todbot/picostepseq/docs/picostepseq_assembly2.jpg

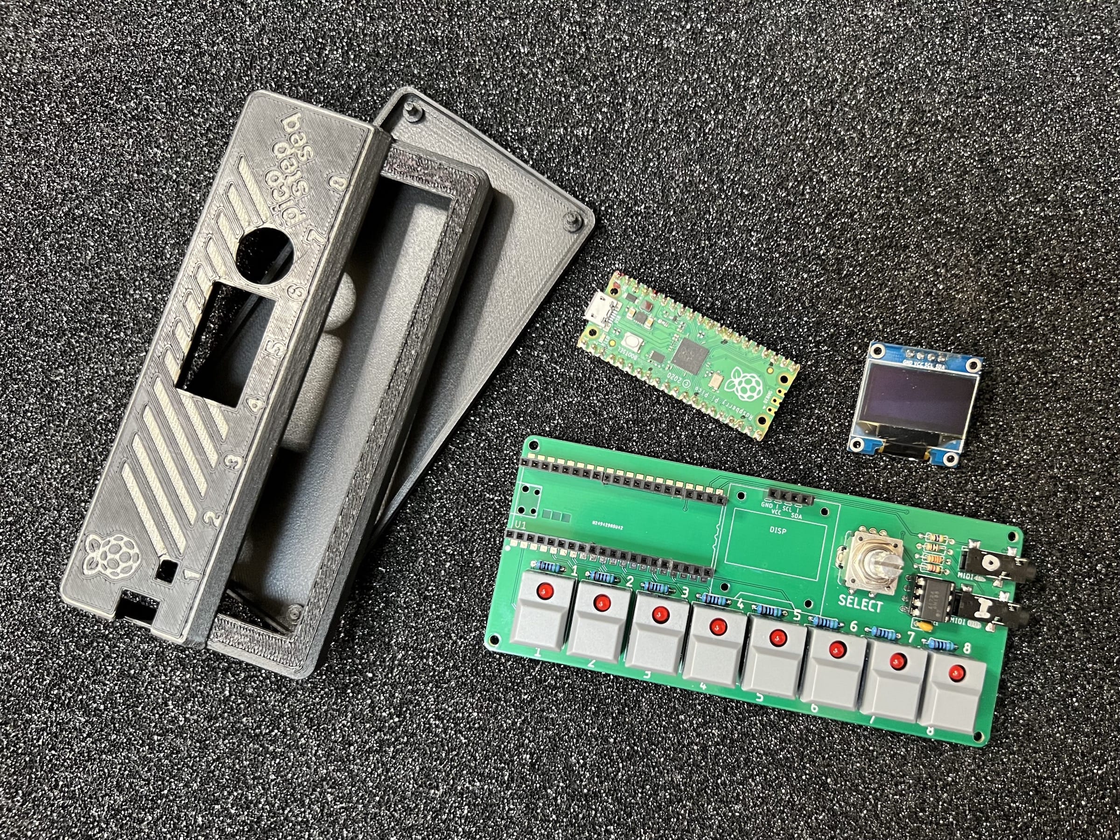
docs/picostepseq_assembly2.jpg
