todbot/picostepseq/docs/picostepseq_assembly3.jpg

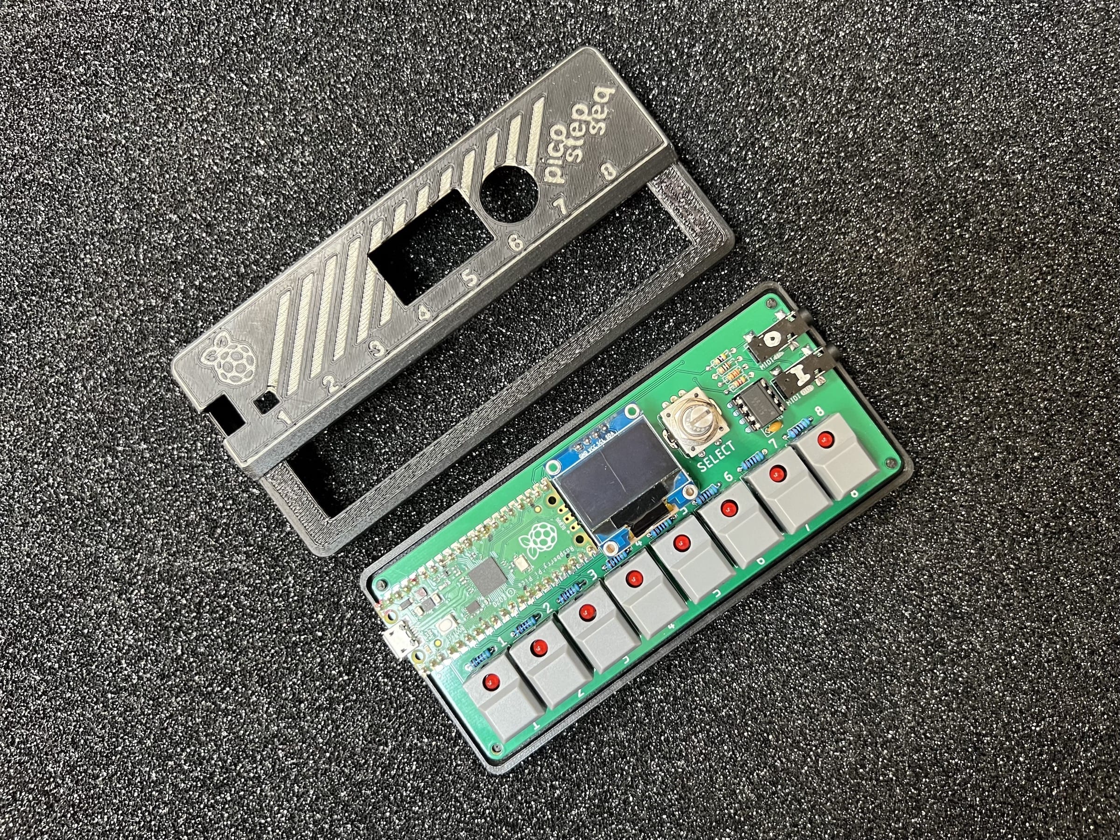
docs/picostepseq_assembly3.jpg
