todbot/picostepseq/circuitpython/picostepseq/winterbloom_smolmidi.py

# The MIT License (MIT)
#
# Copyright (c) 2019 Alethea Flowers for Winterbloom
#
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
__version__ = "0.0.0-auto.0"
__repo__ = "https://github.com/theacodes/Winterbloom_SmolMIDI.git"

"""A minimalist MIDI library."""

# Message type constants.
NOTE_OFF = 0x80
NOTE_ON = 0x90
AFTERTOUCH = 0xA0
CONTROLLER_CHANGE = CC = 0xB0
PROGRAM_CHANGE = 0xC0
CHANNEL_PRESSURE = 0xD0
PITCH_BEND = 0xE0
SYSTEM_EXCLUSIVE = SYSEX = 0xF0
SONG_POSITION = 0xF2
SONG_SELECT = 0xF3
BUS_SELECT = 0xF5
TUNE_REQUEST = 0xF6
SYSEX_END = 0xF7
CLOCK = 0xF8
TICK = 0xF9
START = 0xFA
CONTINUE = 0xFB
STOP = 0xFC
ACTIVE_SENSING = 0xFE
SYSTEM_RESET = 0xFF

_LEN_0_MESSAGES = set(
    [
        TUNE_REQUEST,
        SYSEX,
        SYSEX_END,
        CLOCK,
        TICK,
        START,
        CONTINUE,
        STOP,
        ACTIVE_SENSING,
        SYSTEM_RESET,
    ]
)
_LEN_1_MESSAGES = set([PROGRAM_CHANGE, CHANNEL_PRESSURE, SONG_SELECT, BUS_SELECT])
_LEN_2_MESSAGES = set([NOTE_OFF, NOTE_ON, AFTERTOUCH, CC, PITCH_BEND, SONG_POSITION])


def _is_channel_message(status_byte):
    return status_byte >= NOTE_OFF and status_byte <= PITCH_BEND + 0x0F


def _read_n_bytes(port, buf, dest, num_bytes):
    while num_bytes:
        if port.readinto(buf, 1):
            dest.append(buf[0])
            num_bytes -= 1


class Message:
    def __init__(self):
        self.type = None
        self.channel = None
        self.data = None

    def __bytes__(self):
        status_byte = self.type
        if self.channel:
            status_byte |= self.channel

        return bytes([status_byte] + list(self.data if self.data else []))


class MidiIn:
    def __init__(self, port, enable_running_status=False):
        self._port = port
        self._read_buf = bytearray(3)
        self._running_status_enabled = enable_running_status
        self._running_status = None
        self._outstanding_sysex = False
        self._error_count = 0

    @property
    def error_count(self):
        return self._error_count

    def receive(self):
        # Before we do anything, check and see if there's an unprocessed
        # sysex message pending. If so, throw it away. The caller has
        # to call receive_sysex if they care about the bytes.
        if self._outstanding_sysex:
            self.receive_sysex(0)

        # Read the status byte for the next message.
        result = self._port.readinto(self._read_buf, 1)

        # No message ready.
        if not result:
            return None

        message = Message()
        data_bytes = bytearray()

        # Is this a status byte?
        status_byte = self._read_buf[0]
        is_status = status_byte & 0x80

        # If not, see if we have a running status byte.
        if not is_status:
            if self._running_status_enabled and self._running_status:
                data_bytes = [status_byte]
                status_byte = self._running_status
            # If not a status byte and no running status, this is
            # invalid data.
            else:
                self._error_count += 1
                return None

        # Is this a channel message, if so, let's figure out the right
        # message type and set the message's channel property.
        if _is_channel_message(status_byte):
            # Only set the running status byte for channel messages.
            self._running_status = status_byte
            # Mask off the channel nibble.
            message.type = status_byte & 0xF0
            message.channel = status_byte & 0x0F
        else:
            message.type = status_byte

        # Read the appropriate number of bytes for each message type.
        if message.type in _LEN_2_MESSAGES:
            _read_n_bytes(self._port, self._read_buf, data_bytes, 2 - len(data_bytes))
            message.data = data_bytes
        elif message.type in _LEN_1_MESSAGES:
            _read_n_bytes(self._port, self._read_buf, data_bytes, 1 - len(data_bytes))
            message.data = data_bytes

        # If this is a sysex message, set the pending sysex flag so we
        # can throw the message away if the user doesn't process it.
        if message.type == SYSEX:
            self._outstanding_sysex = True

        # Check the data bytes for corruption. If the data bytes have any status bytes
        # embedded, it probably means the buffer overflowed. Either way, discard the
        # message.
        # TODO: Figure out a better way to detect and deal with this upstream.
        for b in data_bytes:
            if b & 0x80:
                self._error_count += 1
                return None

        return message

    def receive_sysex(self, max_length):
        """Receives the next outstanding sysex message.

        Returns a tuple: the first item is the bytearray of the
        sysex message. The second is a boolean that indicates
        if the message was truncated or not.

        This must only be called after getting a sysex message from
        receive and must be called before invoking receive again.
        """
        self._outstanding_sysex = False

        out = bytearray()
        length = 0
        buf = bytearray(1)
        truncated = False

        # This reads one byte at a time so we don't read past the
        # end byte. There may be more efficient ways to do this
        # but sysex messages should be relatively rare in practice,
        # so I'm not sure how much benefit we'll get.
        while length < max_length:
            self._port.readinto(buf, 1)
            if buf[0] == SYSEX_END:
                break
            out.extend(buf)
            length += 1

        # We exceeded the length.
        else:
            truncated = True
            # Ignore the rest of the message by reading and throwing away
            # bytes until we get to SYSEX_END.
            while buf[0] != SYSEX_END:
                self._port.readinto(buf, 1)

        return out, truncated
