todbot/picostepseq/arduino/picostepseq/saved_sequences_json.h

const char* default_saved_sequences_json = "[[[60, 127, 10, true], [52, 127, 4, false], [60, 127, 8, true], [60, 127, 8, true], [72, 127, 14, true], [46, 127, 8, false], [60, 127, 8, false], [48, 127, 14, true]], [[53, 127, 10, true], [64, 127, 5, true], [65, 127, 4, true], [72, 127, 5, true], [60, 127, 8, true], [48, 127, 7, false], [48, 127, 3, false], [53, 127, 12, true]], [[48, 127, 14, true], [52, 127, 8, false], [67, 127, 8, true], [69, 127, 8, true], [65, 127, 15, true], [55, 127, 14, false], [55, 127, 14, true], [44, 127, 4, true]], [[60, 127, 14, true], [52, 127, 8, false], [69, 127, 8, true], [67, 127, 8, true], [65, 127, 15, true], [55, 127, 14, false], [62, 127, 14, true], [43, 127, 4, false]], [[60, 127, 14, true], [72, 127, 8, false], [67, 127, 8, true], [65, 127, 8, false], [60, 127, 8, true], [36, 127, 14, false], [55, 127, 14, false], [48, 127, 8, true]], [[59, 127, 14, true], [47, 127, 8, false], [67, 127, 8, true], [67, 127, 8, false], [59, 127, 8, true], [47, 127, 14, false], [59, 127, 14, true], [47, 127, 8, false]], [[53, 127, 14, true], [52, 127, 8, false], [53, 127, 8, true], [54, 127, 8, false], [55, 127, 8, true], [56, 127, 14, false], [57, 127, 14, true], [58, 127, 8, false]], [[48, 127, 14, true], [52, 127, 8, false], [53, 127, 8, true], [54, 127, 8, false], [55, 127, 8, true], [56, 127, 14, false], [57, 127, 14, true], [58, 127, 8, false]]]";
